hackingchips/Peugeot-3008-Display/Firmware/PeugeotDisplay4245/PeugeotDisplay4245.cydsn/codegentemp/SPILCD_SPI_UART.c

/***************************************************************************//**
* \file SPILCD_SPI_UART.c
* \version 4.0
*
* \brief
*  This file provides the source code to the API for the SCB Component in
*  SPI and UART modes.
*
* Note:
*
*******************************************************************************
* \copyright
* Copyright 2013-2017, Cypress Semiconductor Corporation.  All rights reserved.
* You may use this file only in accordance with the license, terms, conditions,
* disclaimers, and limitations in the end user license agreement accompanying
* the software package with which this file was provided.
*******************************************************************************/

#include "SPILCD_PVT.h"
#include "SPILCD_SPI_UART_PVT.h"

/***************************************
*        SPI/UART Private Vars
***************************************/

#if(SPILCD_INTERNAL_RX_SW_BUFFER_CONST)
    /* Start index to put data into the software receive buffer.*/
    volatile uint32 SPILCD_rxBufferHead;
    /* Start index to get data from the software receive buffer.*/
    volatile uint32 SPILCD_rxBufferTail;
    /**
    * \addtogroup group_globals
    * \{
    */
    /** Sets when internal software receive buffer overflow
    *  was occurred.
    */
    volatile uint8  SPILCD_rxBufferOverflow;
    /** \} globals */
#endif /* (SPILCD_INTERNAL_RX_SW_BUFFER_CONST) */

#if(SPILCD_INTERNAL_TX_SW_BUFFER_CONST)
    /* Start index to put data into the software transmit buffer.*/
    volatile uint32 SPILCD_txBufferHead;
    /* Start index to get data from the software transmit buffer.*/
    volatile uint32 SPILCD_txBufferTail;
#endif /* (SPILCD_INTERNAL_TX_SW_BUFFER_CONST) */

#if(SPILCD_INTERNAL_RX_SW_BUFFER)
    /* Add one element to the buffer to receive full packet. One byte in receive buffer is always empty */
    volatile uint8 SPILCD_rxBufferInternal[SPILCD_INTERNAL_RX_BUFFER_SIZE];
#endif /* (SPILCD_INTERNAL_RX_SW_BUFFER) */

#if(SPILCD_INTERNAL_TX_SW_BUFFER)
    volatile uint8 SPILCD_txBufferInternal[SPILCD_TX_BUFFER_SIZE];
#endif /* (SPILCD_INTERNAL_TX_SW_BUFFER) */


#if(SPILCD_RX_DIRECTION)
    /*******************************************************************************
    * Function Name: SPILCD_SpiUartReadRxData
    ****************************************************************************//**
    *
    *  Retrieves the next data element from the receive buffer.
    *   - RX software buffer is disabled: Returns data element retrieved from
    *     RX FIFO. Undefined data will be returned if the RX FIFO is empty.
    *   - RX software buffer is enabled: Returns data element from the software
    *     receive buffer. Zero value is returned if the software receive buffer
    *     is empty.
    *
    * \return
    *  Next data element from the receive buffer. 
    *  The amount of data bits to be received depends on RX data bits selection 
    *  (the data bit counting starts from LSB of return value).
    *
    * \globalvars
    *  SPILCD_rxBufferHead - the start index to put data into the 
    *  software receive buffer.
    *  SPILCD_rxBufferTail - the start index to get data from the 
    *  software receive buffer.
    *
    *******************************************************************************/
    uint32 SPILCD_SpiUartReadRxData(void)
    {
        uint32 rxData = 0u;

    #if (SPILCD_INTERNAL_RX_SW_BUFFER_CONST)
        uint32 locTail;
    #endif /* (SPILCD_INTERNAL_RX_SW_BUFFER_CONST) */

        #if (SPILCD_CHECK_RX_SW_BUFFER)
        {
            if (SPILCD_rxBufferHead != SPILCD_rxBufferTail)
            {
                /* There is data in RX software buffer */

                /* Calculate index to read from */
                locTail = (SPILCD_rxBufferTail + 1u);

                if (SPILCD_INTERNAL_RX_BUFFER_SIZE == locTail)
                {
                    locTail = 0u;
                }

                /* Get data from RX software buffer */
                rxData = SPILCD_GetWordFromRxBuffer(locTail);

                /* Change index in the buffer */
                SPILCD_rxBufferTail = locTail;

                #if (SPILCD_CHECK_UART_RTS_CONTROL_FLOW)
                {
                    /* Check if RX Not Empty is disabled in the interrupt */
                    if (0u == (SPILCD_INTR_RX_MASK_REG & SPILCD_INTR_RX_NOT_EMPTY))
                    {
                        /* Enable RX Not Empty interrupt source to continue
                        * receiving data into software buffer.
                        */
                        SPILCD_INTR_RX_MASK_REG |= SPILCD_INTR_RX_NOT_EMPTY;
                    }
                }
                #endif

            }
        }
        #else
        {
            /* Read data from RX FIFO */
            rxData = SPILCD_RX_FIFO_RD_REG;
        }
        #endif

        return (rxData);
    }


    /*******************************************************************************
    * Function Name: SPILCD_SpiUartGetRxBufferSize
    ****************************************************************************//**
    *
    *  Returns the number of received data elements in the receive buffer.
    *   - RX software buffer disabled: returns the number of used entries in
    *     RX FIFO.
    *   - RX software buffer enabled: returns the number of elements which were
    *     placed in the receive buffer. This does not include the hardware RX FIFO.
    *
    * \return
    *  Number of received data elements.
    *
    * \globalvars
    *  SPILCD_rxBufferHead - the start index to put data into the 
    *  software receive buffer.
    *  SPILCD_rxBufferTail - the start index to get data from the 
    *  software receive buffer.
    *
    *******************************************************************************/
    uint32 SPILCD_SpiUartGetRxBufferSize(void)
    {
        uint32 size;
    #if (SPILCD_INTERNAL_RX_SW_BUFFER_CONST)
        uint32 locHead;
    #endif /* (SPILCD_INTERNAL_RX_SW_BUFFER_CONST) */

        #if (SPILCD_CHECK_RX_SW_BUFFER)
        {
            locHead = SPILCD_rxBufferHead;

            if(locHead >= SPILCD_rxBufferTail)
            {
                size = (locHead - SPILCD_rxBufferTail);
            }
            else
            {
                size = (locHead + (SPILCD_INTERNAL_RX_BUFFER_SIZE - SPILCD_rxBufferTail));
            }
        }
        #else
        {
            size = SPILCD_GET_RX_FIFO_ENTRIES;
        }
        #endif

        return (size);
    }


    /*******************************************************************************
    * Function Name: SPILCD_SpiUartClearRxBuffer
    ****************************************************************************//**
    *
    *  Clears the receive buffer and RX FIFO.
    *
    * \globalvars
    *  SPILCD_rxBufferHead - the start index to put data into the 
    *  software receive buffer.
    *  SPILCD_rxBufferTail - the start index to get data from the 
    *  software receive buffer.
    *
    *******************************************************************************/
    void SPILCD_SpiUartClearRxBuffer(void)
    {
        #if (SPILCD_CHECK_RX_SW_BUFFER)
        {
            /* Lock from component interruption */
            SPILCD_DisableInt();

            /* Flush RX software buffer */
            SPILCD_rxBufferHead = SPILCD_rxBufferTail;
            SPILCD_rxBufferOverflow = 0u;

            SPILCD_CLEAR_RX_FIFO;
            SPILCD_ClearRxInterruptSource(SPILCD_INTR_RX_ALL);

            #if (SPILCD_CHECK_UART_RTS_CONTROL_FLOW)
            {
                /* Enable RX Not Empty interrupt source to continue receiving
                * data into software buffer.
                */
                SPILCD_INTR_RX_MASK_REG |= SPILCD_INTR_RX_NOT_EMPTY;
            }
            #endif
            
            /* Release lock */
            SPILCD_EnableInt();
        }
        #else
        {
            SPILCD_CLEAR_RX_FIFO;
        }
        #endif
    }

#endif /* (SPILCD_RX_DIRECTION) */


#if(SPILCD_TX_DIRECTION)
    /*******************************************************************************
    * Function Name: SPILCD_SpiUartWriteTxData
    ****************************************************************************//**
    *
    *  Places a data entry into the transmit buffer to be sent at the next available
    *  bus time.
    *  This function is blocking and waits until there is space available to put the
    *  requested data in the transmit buffer.
    *
    *  \param txDataByte: the data to be transmitted.
    *   The amount of data bits to be transmitted depends on TX data bits selection 
    *   (the data bit counting starts from LSB of txDataByte).
    *
    * \globalvars
    *  SPILCD_txBufferHead - the start index to put data into the 
    *  software transmit buffer.
    *  SPILCD_txBufferTail - start index to get data from the software
    *  transmit buffer.
    *
    *******************************************************************************/
    void SPILCD_SpiUartWriteTxData(uint32 txData)
    {
    #if (SPILCD_INTERNAL_TX_SW_BUFFER_CONST)
        uint32 locHead;
    #endif /* (SPILCD_INTERNAL_TX_SW_BUFFER_CONST) */

        #if (SPILCD_CHECK_TX_SW_BUFFER)
        {
            /* Put data directly into the TX FIFO */
            if ((SPILCD_txBufferHead == SPILCD_txBufferTail) &&
                (SPILCD_SPI_UART_FIFO_SIZE != SPILCD_GET_TX_FIFO_ENTRIES))
            {
                /* TX software buffer is empty: put data directly in TX FIFO */
                SPILCD_TX_FIFO_WR_REG = txData;
            }
            /* Put data into TX software buffer */
            else
            {
                /* Head index to put data */
                locHead = (SPILCD_txBufferHead + 1u);

                /* Adjust TX software buffer index */
                if (SPILCD_TX_BUFFER_SIZE == locHead)
                {
                    locHead = 0u;
                }

                /* Wait for space in TX software buffer */
                while (locHead == SPILCD_txBufferTail)
                {
                }

                /* TX software buffer has at least one room */

                /* Clear old status of INTR_TX_NOT_FULL. It sets at the end of transfer when TX FIFO is empty. */
                SPILCD_ClearTxInterruptSource(SPILCD_INTR_TX_NOT_FULL);

                SPILCD_PutWordInTxBuffer(locHead, txData);

                SPILCD_txBufferHead = locHead;

                /* Check if TX Not Full is disabled in interrupt */
                if (0u == (SPILCD_INTR_TX_MASK_REG & SPILCD_INTR_TX_NOT_FULL))
                {
                    /* Enable TX Not Full interrupt source to transmit from software buffer */
                    SPILCD_INTR_TX_MASK_REG |= (uint32) SPILCD_INTR_TX_NOT_FULL;
                }
            }
        }
        #else
        {
            /* Wait until TX FIFO has space to put data element */
            while (SPILCD_SPI_UART_FIFO_SIZE == SPILCD_GET_TX_FIFO_ENTRIES)
            {
            }

            SPILCD_TX_FIFO_WR_REG = txData;
        }
        #endif
    }


    /*******************************************************************************
    * Function Name: SPILCD_SpiUartPutArray
    ****************************************************************************//**
    *
    *  Places an array of data into the transmit buffer to be sent.
    *  This function is blocking and waits until there is a space available to put
    *  all the requested data in the transmit buffer. The array size can be greater
    *  than transmit buffer size.
    *
    * \param wrBuf: pointer to an array of data to be placed in transmit buffer. 
    *  The width of the data to be transmitted depends on TX data width selection 
    *  (the data bit counting starts from LSB for each array element).
    * \param count: number of data elements to be placed in the transmit buffer.
    *
    * \globalvars
    *  SPILCD_txBufferHead - the start index to put data into the 
    *  software transmit buffer.
    *  SPILCD_txBufferTail - start index to get data from the software
    *  transmit buffer.
    *
    *******************************************************************************/
    void SPILCD_SpiUartPutArray(const uint8 wrBuf[], uint32 count)
    {
        uint32 i;

        for (i=0u; i < count; i++)
        {
            SPILCD_SpiUartWriteTxData((uint32) wrBuf[i]);
        }
    }


    /*******************************************************************************
    * Function Name: SPILCD_SpiUartGetTxBufferSize
    ****************************************************************************//**
    *
    *  Returns the number of elements currently in the transmit buffer.
    *   - TX software buffer is disabled: returns the number of used entries in
    *     TX FIFO.
    *   - TX software buffer is enabled: returns the number of elements currently
    *     used in the transmit buffer. This number does not include used entries in
    *     the TX FIFO. The transmit buffer size is zero until the TX FIFO is
    *     not full.
    *
    * \return
    *  Number of data elements ready to transmit.
    *
    * \globalvars
    *  SPILCD_txBufferHead - the start index to put data into the 
    *  software transmit buffer.
    *  SPILCD_txBufferTail - start index to get data from the software
    *  transmit buffer.
    *
    *******************************************************************************/
    uint32 SPILCD_SpiUartGetTxBufferSize(void)
    {
        uint32 size;
    #if (SPILCD_INTERNAL_TX_SW_BUFFER_CONST)
        uint32 locTail;
    #endif /* (SPILCD_INTERNAL_TX_SW_BUFFER_CONST) */

        #if (SPILCD_CHECK_TX_SW_BUFFER)
        {
            /* Get current Tail index */
            locTail = SPILCD_txBufferTail;

            if (SPILCD_txBufferHead >= locTail)
            {
                size = (SPILCD_txBufferHead - locTail);
            }
            else
            {
                size = (SPILCD_txBufferHead + (SPILCD_TX_BUFFER_SIZE - locTail));
            }
        }
        #else
        {
            size = SPILCD_GET_TX_FIFO_ENTRIES;
        }
        #endif

        return (size);
    }


    /*******************************************************************************
    * Function Name: SPILCD_SpiUartClearTxBuffer
    ****************************************************************************//**
    *
    *  Clears the transmit buffer and TX FIFO.
    *
    * \globalvars
    *  SPILCD_txBufferHead - the start index to put data into the 
    *  software transmit buffer.
    *  SPILCD_txBufferTail - start index to get data from the software
    *  transmit buffer.
    *
    *******************************************************************************/
    void SPILCD_SpiUartClearTxBuffer(void)
    {
        #if (SPILCD_CHECK_TX_SW_BUFFER)
        {
            /* Lock from component interruption */
            SPILCD_DisableInt();

            /* Flush TX software buffer */
            SPILCD_txBufferHead = SPILCD_txBufferTail;

            SPILCD_INTR_TX_MASK_REG &= (uint32) ~SPILCD_INTR_TX_NOT_FULL;
            SPILCD_CLEAR_TX_FIFO;
            SPILCD_ClearTxInterruptSource(SPILCD_INTR_TX_ALL);

            /* Release lock */
            SPILCD_EnableInt();
        }
        #else
        {
            SPILCD_CLEAR_TX_FIFO;
        }
        #endif
    }

#endif /* (SPILCD_TX_DIRECTION) */


/*******************************************************************************
* Function Name: SPILCD_SpiUartDisableIntRx
****************************************************************************//**
*
*  Disables the RX interrupt sources.
*
*  \return
*   Returns the RX interrupt sources enabled before the function call.
*
*******************************************************************************/
uint32 SPILCD_SpiUartDisableIntRx(void)
{
    uint32 intSource;

    intSource = SPILCD_GetRxInterruptMode();

    SPILCD_SetRxInterruptMode(SPILCD_NO_INTR_SOURCES);

    return (intSource);
}


/*******************************************************************************
* Function Name: SPILCD_SpiUartDisableIntTx
****************************************************************************//**
*
*  Disables TX interrupt sources.
*
*  \return
*   Returns TX interrupt sources enabled before function call.
*
*******************************************************************************/
uint32 SPILCD_SpiUartDisableIntTx(void)
{
    uint32 intSourceMask;

    intSourceMask = SPILCD_GetTxInterruptMode();

    SPILCD_SetTxInterruptMode(SPILCD_NO_INTR_SOURCES);

    return (intSourceMask);
}


#if(SPILCD_SCB_MODE_UNCONFIG_CONST_CFG)
    /*******************************************************************************
    * Function Name: SPILCD_PutWordInRxBuffer
    ****************************************************************************//**
    *
    *  Stores a byte/word into the RX buffer.
    *  Only available in the Unconfigured operation mode.
    *
    *  \param index:      index to store data byte/word in the RX buffer.
    *  \param rxDataByte: byte/word to store.
    *
    *******************************************************************************/
    void SPILCD_PutWordInRxBuffer(uint32 idx, uint32 rxDataByte)
    {
        /* Put data in buffer */
        if (SPILCD_ONE_BYTE_WIDTH == SPILCD_rxDataBits)
        {
            SPILCD_rxBuffer[idx] = ((uint8) rxDataByte);
        }
        else
        {
            SPILCD_rxBuffer[(uint32)(idx << 1u)]      = LO8(LO16(rxDataByte));
            SPILCD_rxBuffer[(uint32)(idx << 1u) + 1u] = HI8(LO16(rxDataByte));
        }
    }


    /*******************************************************************************
    * Function Name: SPILCD_GetWordFromRxBuffer
    ****************************************************************************//**
    *
    *  Reads byte/word from RX buffer.
    *  Only available in the Unconfigured operation mode.
    *
    *  \return
    *   Returns byte/word read from RX buffer.
    *
    *******************************************************************************/
    uint32 SPILCD_GetWordFromRxBuffer(uint32 idx)
    {
        uint32 value;

        if (SPILCD_ONE_BYTE_WIDTH == SPILCD_rxDataBits)
        {
            value = SPILCD_rxBuffer[idx];
        }
        else
        {
            value  = (uint32) SPILCD_rxBuffer[(uint32)(idx << 1u)];
            value |= (uint32) ((uint32)SPILCD_rxBuffer[(uint32)(idx << 1u) + 1u] << 8u);
        }

        return (value);
    }


    /*******************************************************************************
    * Function Name: SPILCD_PutWordInTxBuffer
    ****************************************************************************//**
    *
    *  Stores byte/word into the TX buffer.
    *  Only available in the Unconfigured operation mode.
    *
    *  \param idx:        index to store data byte/word in the TX buffer.
    *  \param txDataByte: byte/word to store.
    *
    *******************************************************************************/
    void SPILCD_PutWordInTxBuffer(uint32 idx, uint32 txDataByte)
    {
        /* Put data in buffer */
        if (SPILCD_ONE_BYTE_WIDTH == SPILCD_txDataBits)
        {
            SPILCD_txBuffer[idx] = ((uint8) txDataByte);
        }
        else
        {
            SPILCD_txBuffer[(uint32)(idx << 1u)]      = LO8(LO16(txDataByte));
            SPILCD_txBuffer[(uint32)(idx << 1u) + 1u] = HI8(LO16(txDataByte));
        }
    }


    /*******************************************************************************
    * Function Name: SPILCD_GetWordFromTxBuffer
    ****************************************************************************//**
    *
    *  Reads byte/word from the TX buffer.
    *  Only available in the Unconfigured operation mode.
    *
    *  \param idx: index to get data byte/word from the TX buffer.
    *
    *  \return
    *   Returns byte/word read from the TX buffer.
    *
    *******************************************************************************/
    uint32 SPILCD_GetWordFromTxBuffer(uint32 idx)
    {
        uint32 value;

        if (SPILCD_ONE_BYTE_WIDTH == SPILCD_txDataBits)
        {
            value = (uint32) SPILCD_txBuffer[idx];
        }
        else
        {
            value  = (uint32) SPILCD_txBuffer[(uint32)(idx << 1u)];
            value |= (uint32) ((uint32) SPILCD_txBuffer[(uint32)(idx << 1u) + 1u] << 8u);
        }

        return (value);
    }

#endif /* (SPILCD_SCB_MODE_UNCONFIG_CONST_CFG) */


/* [] END OF FILE */
