hackingchips/Peugeot-3008-Display/Firmware/PeugeotDisplay4245/PeugeotDisplay4245.cydsn/codegentemp/ISR_Capture.h

/*******************************************************************************
* File Name: ISR_Capture.h
* Version 1.70
*
*  Description:
*   Provides the function definitions for the Interrupt Controller.
*
*
********************************************************************************
* Copyright 2008-2015, Cypress Semiconductor Corporation.  All rights reserved.
* You may use this file only in accordance with the license, terms, conditions, 
* disclaimers, and limitations in the end user license agreement accompanying 
* the software package with which this file was provided.
*******************************************************************************/
#if !defined(CY_ISR_ISR_Capture_H)
#define CY_ISR_ISR_Capture_H


#include <cytypes.h>
#include <cyfitter.h>

/* Interrupt Controller API. */
void ISR_Capture_Start(void);
void ISR_Capture_StartEx(cyisraddress address);
void ISR_Capture_Stop(void);

CY_ISR_PROTO(ISR_Capture_Interrupt);

void ISR_Capture_SetVector(cyisraddress address);
cyisraddress ISR_Capture_GetVector(void);

void ISR_Capture_SetPriority(uint8 priority);
uint8 ISR_Capture_GetPriority(void);

void ISR_Capture_Enable(void);
uint8 ISR_Capture_GetState(void);
void ISR_Capture_Disable(void);

void ISR_Capture_SetPending(void);
void ISR_Capture_ClearPending(void);


/* Interrupt Controller Constants */

/* Address of the INTC.VECT[x] register that contains the Address of the ISR_Capture ISR. */
#define ISR_Capture_INTC_VECTOR            ((reg32 *) ISR_Capture__INTC_VECT)

/* Address of the ISR_Capture ISR priority. */
#define ISR_Capture_INTC_PRIOR             ((reg32 *) ISR_Capture__INTC_PRIOR_REG)

/* Priority of the ISR_Capture interrupt. */
#define ISR_Capture_INTC_PRIOR_NUMBER      ISR_Capture__INTC_PRIOR_NUM

/* Address of the INTC.SET_EN[x] byte to bit enable ISR_Capture interrupt. */
#define ISR_Capture_INTC_SET_EN            ((reg32 *) ISR_Capture__INTC_SET_EN_REG)

/* Address of the INTC.CLR_EN[x] register to bit clear the ISR_Capture interrupt. */
#define ISR_Capture_INTC_CLR_EN            ((reg32 *) ISR_Capture__INTC_CLR_EN_REG)

/* Address of the INTC.SET_PD[x] register to set the ISR_Capture interrupt state to pending. */
#define ISR_Capture_INTC_SET_PD            ((reg32 *) ISR_Capture__INTC_SET_PD_REG)

/* Address of the INTC.CLR_PD[x] register to clear the ISR_Capture interrupt. */
#define ISR_Capture_INTC_CLR_PD            ((reg32 *) ISR_Capture__INTC_CLR_PD_REG)



#endif /* CY_ISR_ISR_Capture_H */


/* [] END OF FILE */
