hackingchips/Peugeot-3008-Display/Firmware/PeugeotDisplay4245/PeugeotDisplay4245.cydsn/codegentemp/ISR_Reset.h

/*******************************************************************************
* File Name: ISR_Reset.h
* Version 1.70
*
*  Description:
*   Provides the function definitions for the Interrupt Controller.
*
*
********************************************************************************
* Copyright 2008-2015, Cypress Semiconductor Corporation.  All rights reserved.
* You may use this file only in accordance with the license, terms, conditions, 
* disclaimers, and limitations in the end user license agreement accompanying 
* the software package with which this file was provided.
*******************************************************************************/
#if !defined(CY_ISR_ISR_Reset_H)
#define CY_ISR_ISR_Reset_H


#include <cytypes.h>
#include <cyfitter.h>

/* Interrupt Controller API. */
void ISR_Reset_Start(void);
void ISR_Reset_StartEx(cyisraddress address);
void ISR_Reset_Stop(void);

CY_ISR_PROTO(ISR_Reset_Interrupt);

void ISR_Reset_SetVector(cyisraddress address);
cyisraddress ISR_Reset_GetVector(void);

void ISR_Reset_SetPriority(uint8 priority);
uint8 ISR_Reset_GetPriority(void);

void ISR_Reset_Enable(void);
uint8 ISR_Reset_GetState(void);
void ISR_Reset_Disable(void);

void ISR_Reset_SetPending(void);
void ISR_Reset_ClearPending(void);


/* Interrupt Controller Constants */

/* Address of the INTC.VECT[x] register that contains the Address of the ISR_Reset ISR. */
#define ISR_Reset_INTC_VECTOR            ((reg32 *) ISR_Reset__INTC_VECT)

/* Address of the ISR_Reset ISR priority. */
#define ISR_Reset_INTC_PRIOR             ((reg32 *) ISR_Reset__INTC_PRIOR_REG)

/* Priority of the ISR_Reset interrupt. */
#define ISR_Reset_INTC_PRIOR_NUMBER      ISR_Reset__INTC_PRIOR_NUM

/* Address of the INTC.SET_EN[x] byte to bit enable ISR_Reset interrupt. */
#define ISR_Reset_INTC_SET_EN            ((reg32 *) ISR_Reset__INTC_SET_EN_REG)

/* Address of the INTC.CLR_EN[x] register to bit clear the ISR_Reset interrupt. */
#define ISR_Reset_INTC_CLR_EN            ((reg32 *) ISR_Reset__INTC_CLR_EN_REG)

/* Address of the INTC.SET_PD[x] register to set the ISR_Reset interrupt state to pending. */
#define ISR_Reset_INTC_SET_PD            ((reg32 *) ISR_Reset__INTC_SET_PD_REG)

/* Address of the INTC.CLR_PD[x] register to clear the ISR_Reset interrupt. */
#define ISR_Reset_INTC_CLR_PD            ((reg32 *) ISR_Reset__INTC_CLR_PD_REG)



#endif /* CY_ISR_ISR_Reset_H */


/* [] END OF FILE */
